expertslive/5-years-speaker-lamp/wled/wled-ui-bg-expertslive.jpg

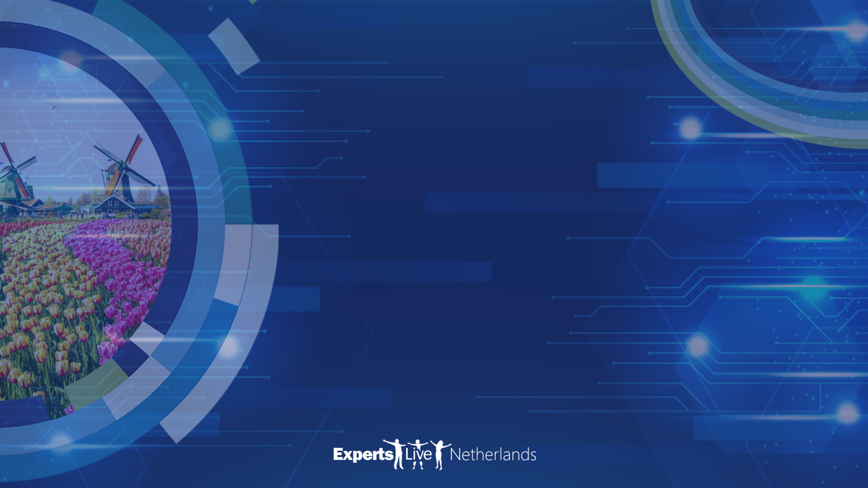
wled/wled-ui-bg-expertslive.jpg
