expertslive/5-years-speaker-lamp/model-files/experts-live-high-five-hive-3-cube-holder.stl

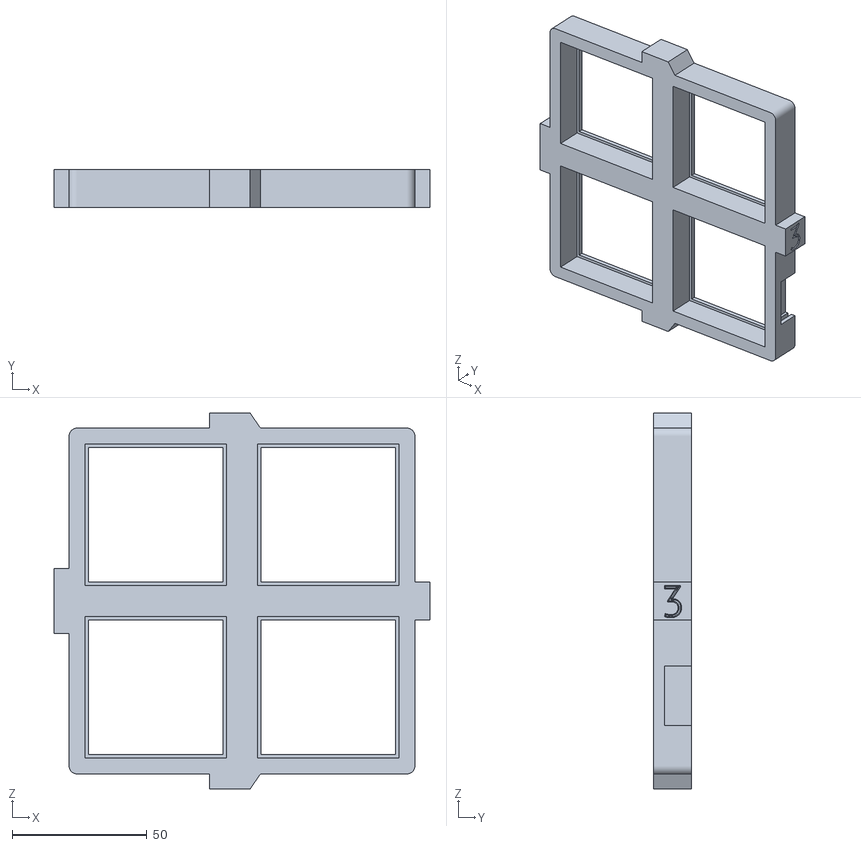
[picture p31: CAD file, 2026-03-17]
model-files/experts-live-high-five-hive-3-cube-holder.stl
139.6 x 14.0 x 139.6
