expertslive/5-years-speaker-lamp/model-files/experts-live-high-five-hive-housing-cover-14-A.stl

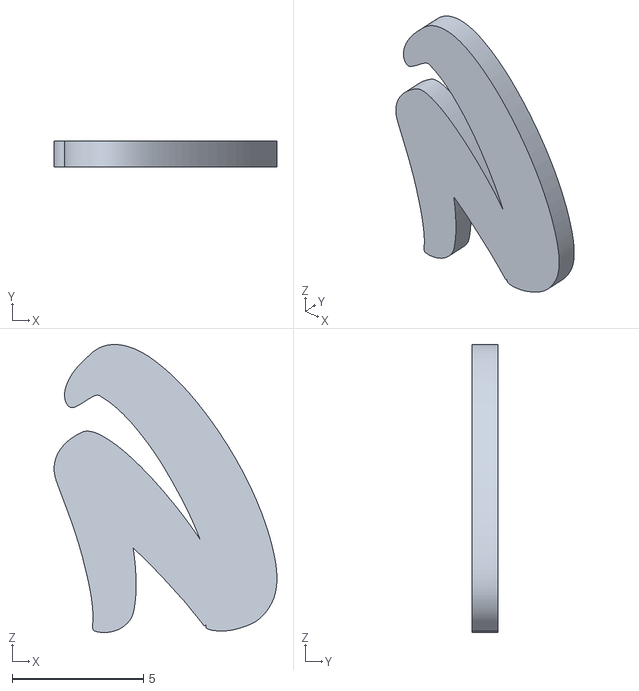
[picture p32: CAD file, 2026-03-17]
model-files/experts-live-high-five-hive-housing-cover-14-A.stl
8.48 x 1.00 x 11.0
