expertslive/5-years-speaker-lamp/model-files/experts-live-high-five-hive-housing-cover-10-mascotte-2-1.stl

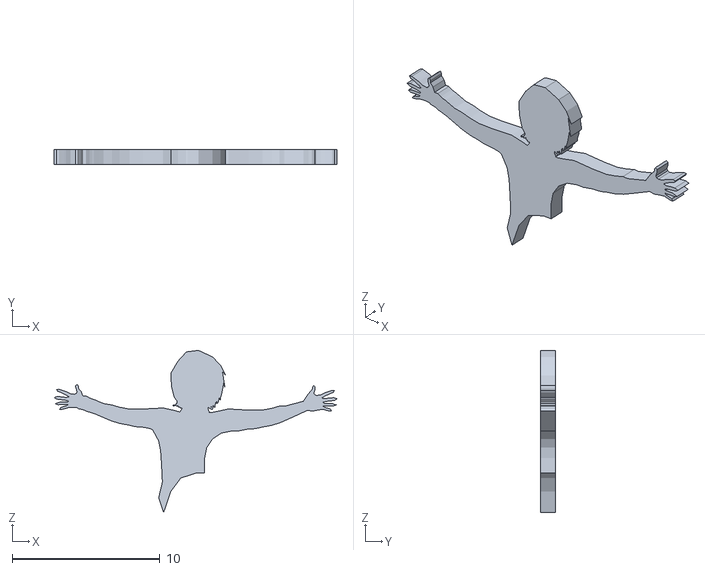
[picture p33: CAD file, 2026-03-17]
model-files/experts-live-high-five-hive-housing-cover-10-mascotte-2-1.stl
19.1 x 1.00 x 11.0
