expertslive/5-years-speaker-lamp/model-files/experts-live-high-five-hive-housing-cover-02-p.stl

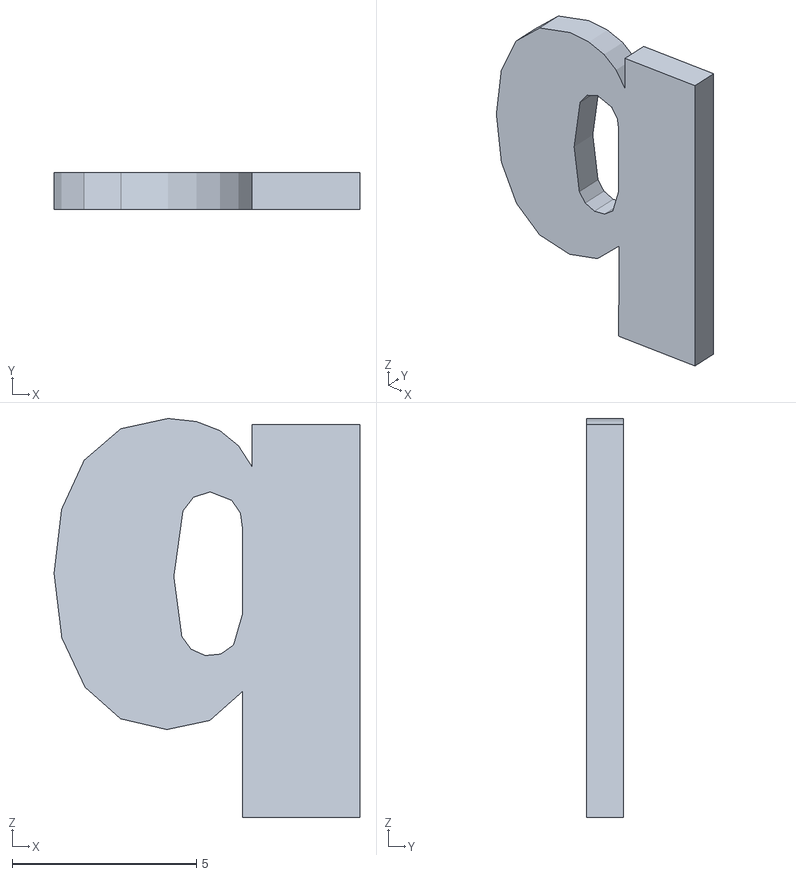
[picture p34: CAD file, 2026-03-17]
model-files/experts-live-high-five-hive-housing-cover-02-p.stl
8.30 x 1.00 x 10.8
