expertslive/5-years-speaker-lamp/model-files/experts-live-high-five-hive-housing-cover-10-mascotte-2-3.stl

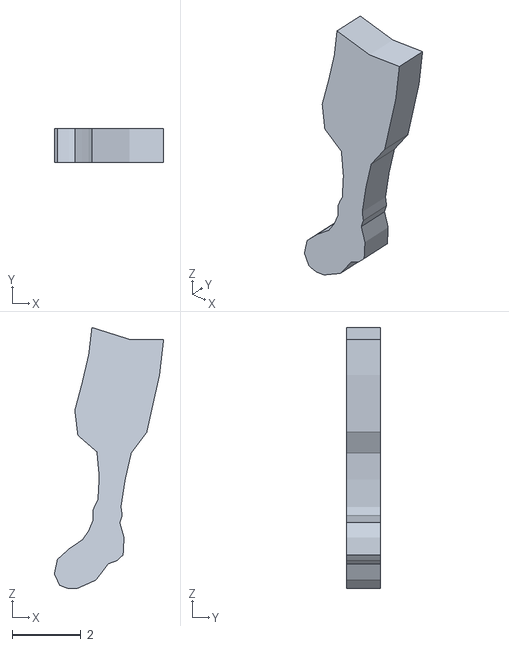
[picture p35: CAD file, 2026-03-17]
model-files/experts-live-high-five-hive-housing-cover-10-mascotte-2-3.stl
3.19 x 1.00 x 7.61
