expertslive/5-years-speaker-lamp/model-files/experts-live-high-five-hive-2-led-frame.stl

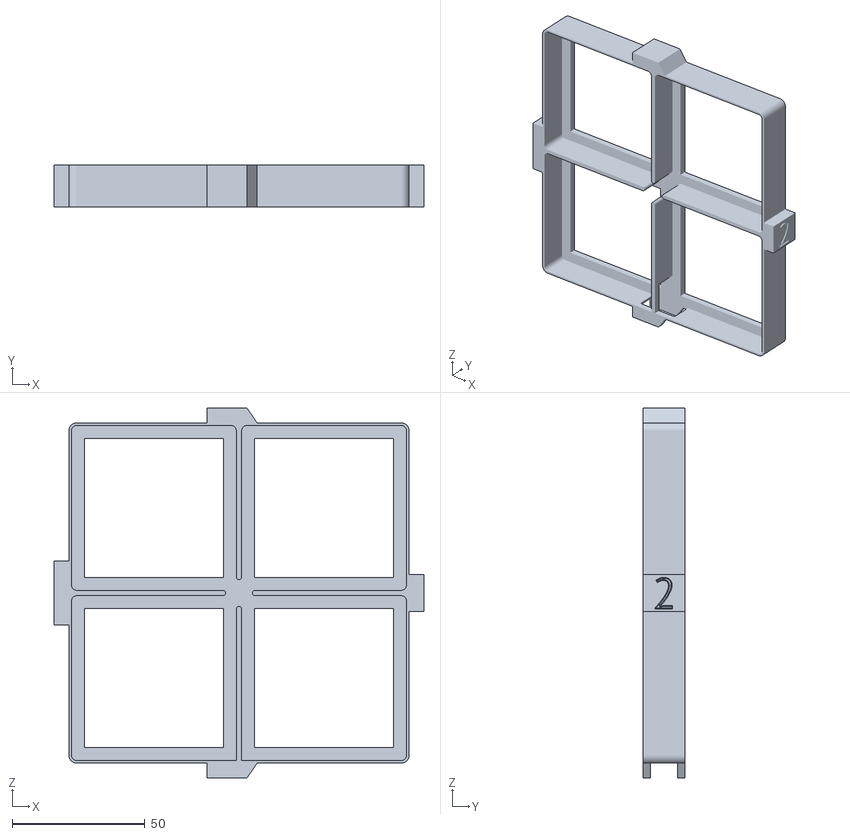
[picture p36: CAD file, 2026-03-17]
model-files/experts-live-high-five-hive-2-led-frame.stl
139.6 x 16.0 x 139.6
