expertslive/5-years-speaker-lamp/model-files/experts-live-high-five-hive-housing-cover.stl

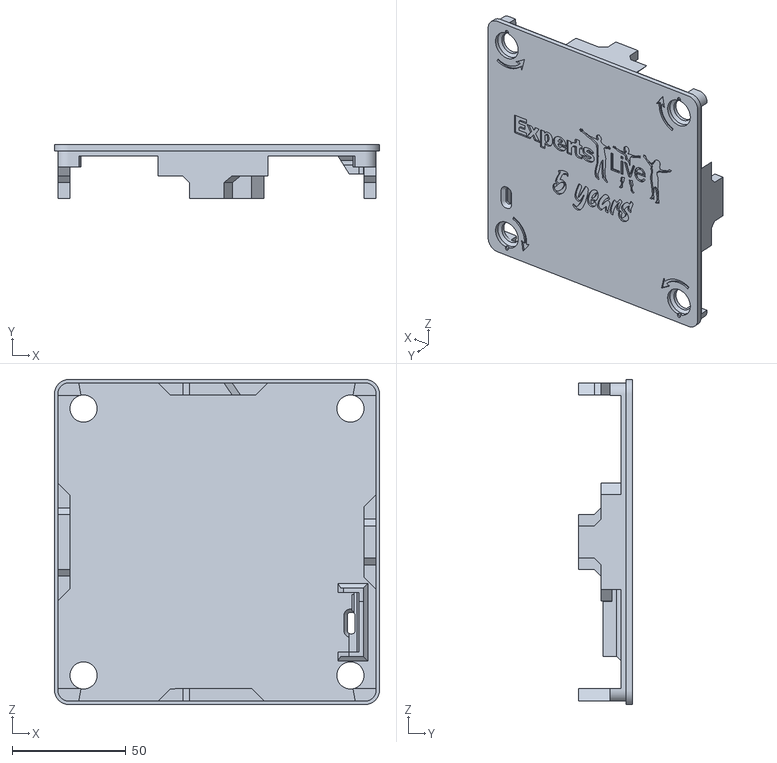
[picture p37: CAD file, 2026-03-17]
model-files/experts-live-high-five-hive-housing-cover.stl
142.6 x 23.8 x 142.6
