expertslive/5-years-speaker-lamp/model-files/experts-live-high-five-hive-housing-cover-06-l.stl

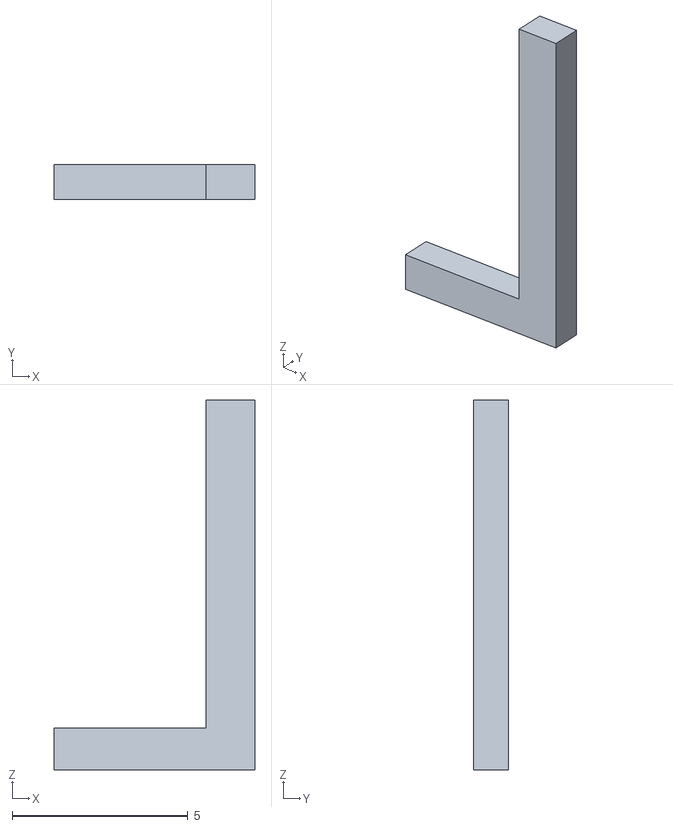
[picture p38: CAD file, 2026-03-17]
model-files/experts-live-high-five-hive-housing-cover-06-l.stl
5.72 x 1.00 x 10.5
