expertslive/5-years-speaker-lamp/model-files/experts-live-high-five-hive-housing-cover-03-e.stl

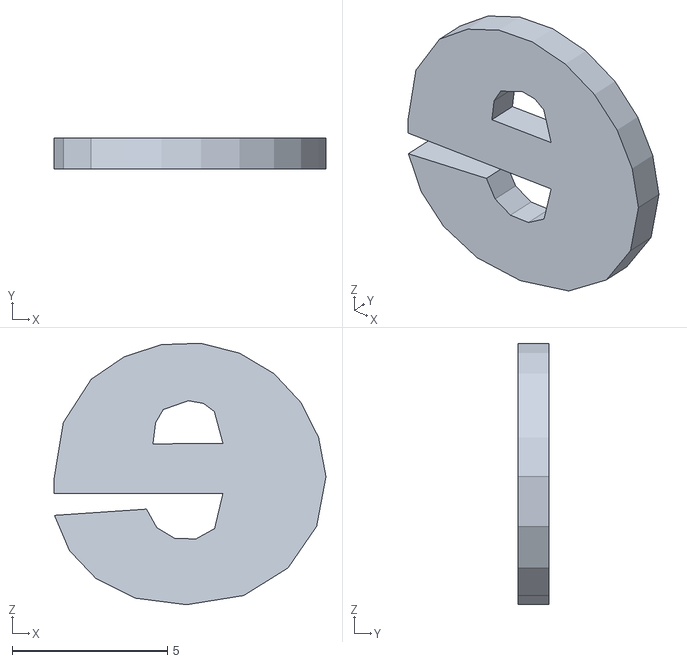
[picture p39: CAD file, 2026-03-17]
model-files/experts-live-high-five-hive-housing-cover-03-e.stl
8.76 x 1.00 x 8.42
