expertslive/5-years-speaker-lamp/model-files/experts-live-high-five-hive-housing-cover-11-5.stl

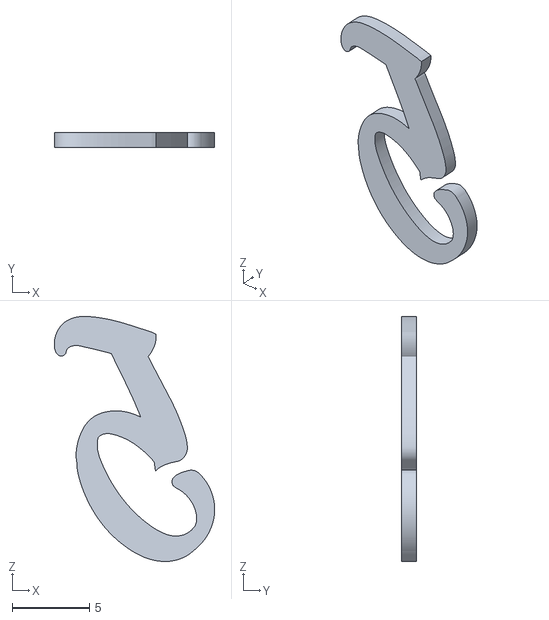
[picture p40: CAD file, 2026-03-17]
model-files/experts-live-high-five-hive-housing-cover-11-5.stl
10.4 x 1.00 x 15.9
