expertslive/5-years-speaker-lamp/model-files/experts-live-high-five-hive-3-cube-holder-plate.stl

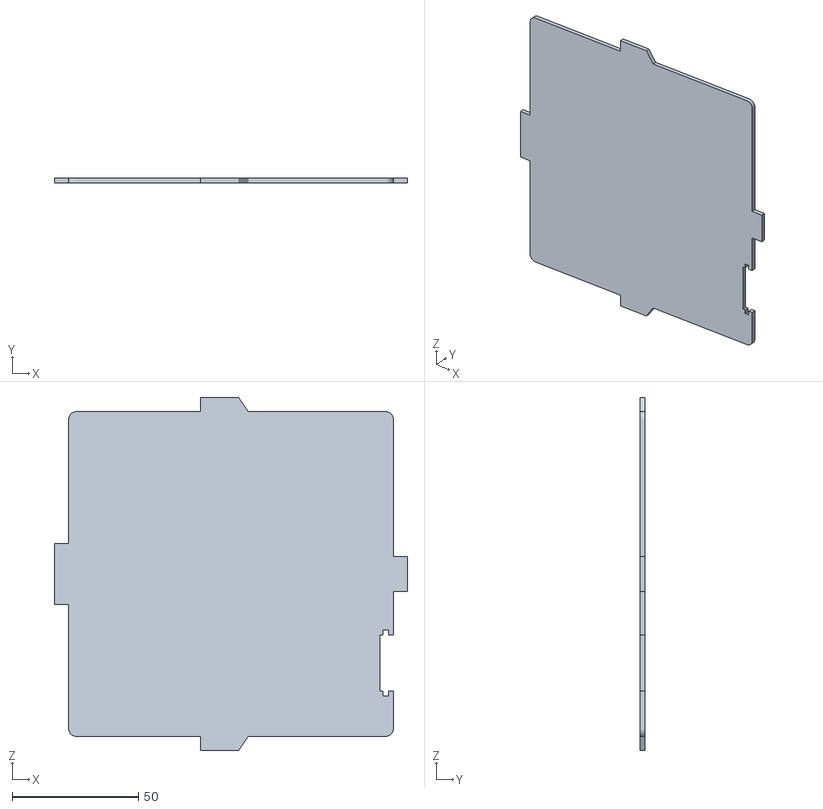
[picture p41: CAD file, 2026-03-17]
model-files/experts-live-high-five-hive-3-cube-holder-plate.stl
139.6 x 2.00 x 139.6
