expertslive/5-years-speaker-lamp/model-files/experts-live-high-five-hive-housing-cover-16-S.stl

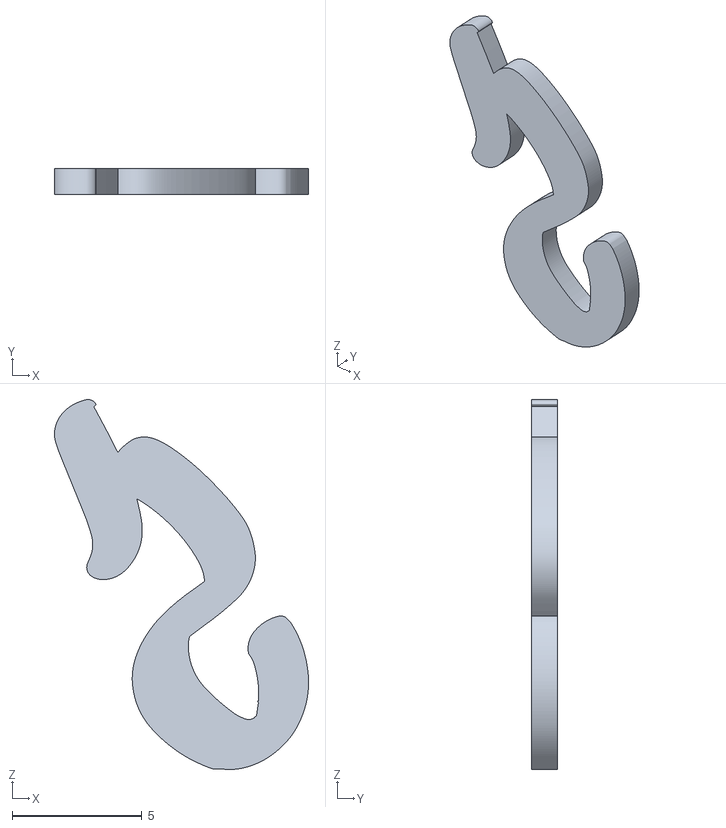
[picture p42: CAD file, 2026-03-17]
model-files/experts-live-high-five-hive-housing-cover-16-S.stl
9.80 x 1.00 x 14.3
