expertslive/5-years-speaker-lamp/model-files/experts-live-high-five-hive-housing-cover-12-Y.stl

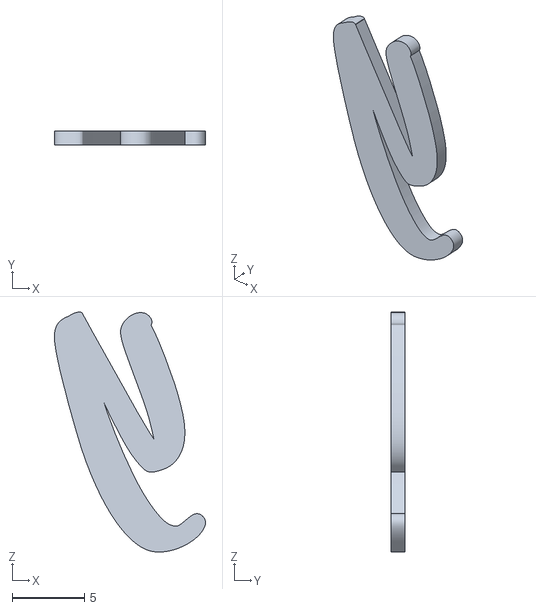
[picture p43: CAD file, 2026-03-17]
model-files/experts-live-high-five-hive-housing-cover-12-Y.stl
10.5 x 1.00 x 16.6
