expertslive/5-years-speaker-lamp/model-files/experts-live-high-five-hive-housing-cover-15-R.stl

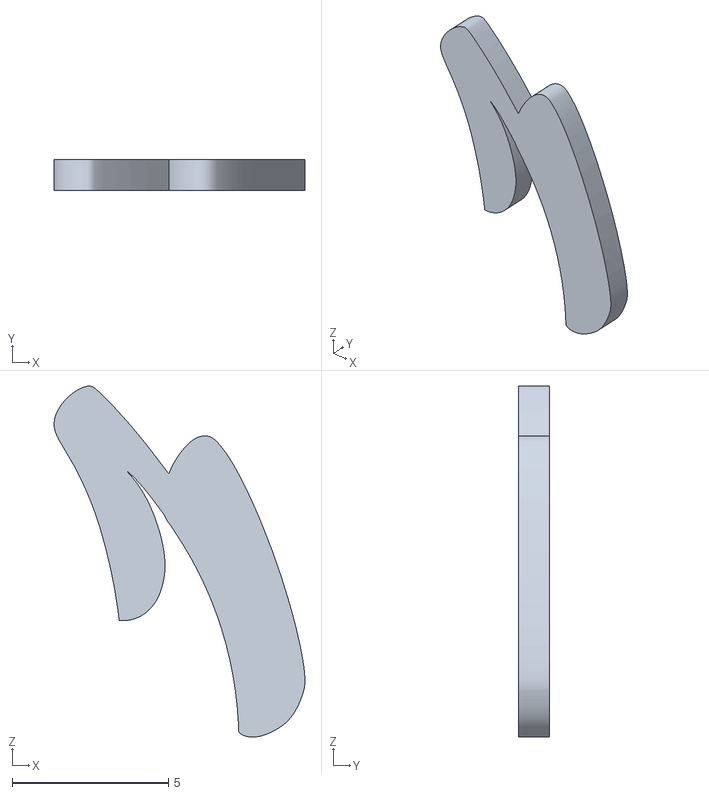
[picture p44: CAD file, 2026-03-17]
model-files/experts-live-high-five-hive-housing-cover-15-R.stl
8.03 x 1.00 x 11.2
